N57WH/mqtt-battery-monitor/src/secrets.h

// ============================================================
// secrets.h — Edit these values for your network
// ============================================================
// This file is included by the main sketch. Keep it out of
// version control if you share your code.
// ============================================================

#define WIFI_SSID       "your_wifi_ssid"
#define WIFI_PASS       "your_wifi_password"

#define MQTT_SERVER     "192.168.1.100"    // your Mosquitto broker IP
#define MQTT_PORT       1883
#define MQTT_USER       "mqtt_user"        // leave "" if no auth
#define MQTT_PASS       "mqtt_password"    // leave "" if no auth

#define OTA_PASSWORD    "ota"       // password for OTA updates
